m9cd0n9ld/IMU-VR-Full-Body-Tracker/hardware example/TTGO-T7-V1.5_GY-BNO08X_expansion-board/TTGO-T7-V1.5_BNO085_expansion-board.sch

## KiCad design hardware example/TTGO-T7-V1.5_GY-BNO08X_expansion-board/TTGO-T7-V1.5_BNO085_expansion-board.sch (2021-06-28)

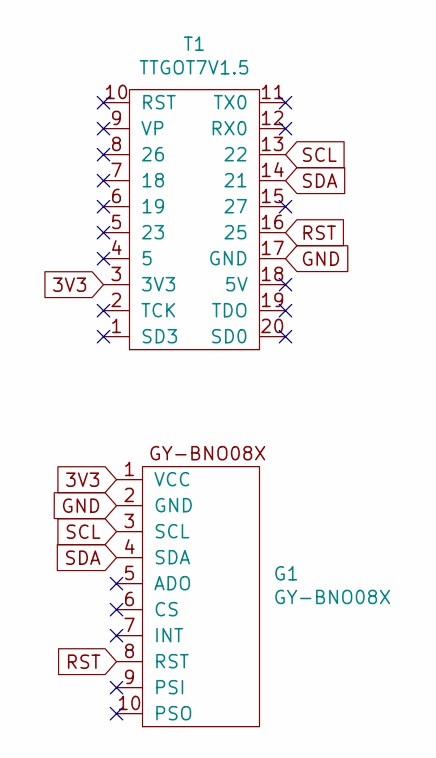
[picture p28: schematic TTGO-T7-V1.5_BNO085_expansion-board.sch]

Parts:
G1: GY-BNO08X
T1: TTGOT7V1.5; TTGO_T7_V1.5

Connections:
3V3: G1.1 (VCC), T1.3 (3V3)
GND: G1.2 (GND), T1.17 (GND)
RST: G1.8 (RST), T1.16 (25)
SCL: G1.3 (SCL), T1.13 (22)
SDA: G1.4 (SDA), T1.14 (21)
