m9cd0n9ld/IMU-VR-Full-Body-Tracker/desktop_server/main.py

import os
import sys
def resource_path(file):
    try:
        directory = os.path.abspath(sys._MEIPASS)
    except:
        directory = os.path.abspath('.')
    return os.path.join(directory, file)

from kivy.config import Config
Config.set('graphics', 'maxfps', '5000')
Config.set('input', 'mouse', 'mouse,disable_multitouch')
Config.set('graphics', 'width', '900')
Config.set('graphics', 'height', '700')
Config.set('graphics', 'minimum_width', '900')
Config.set('graphics', 'minimum_height', '700')
Config.set('kivy', 'window_icon', resource_path('icon.png'))
from kivy.app import App
from kivy.lang import Builder
from kivy.uix.boxlayout import BoxLayout
from kivy.uix.floatlayout import FloatLayout
from kivy.uix.popup import Popup
from kivy.uix.label import Label
from kivy.uix.spinner import Spinner
from kivy.uix.switch import Switch
from kivy.uix.tabbedpanel import TabbedPanel, TabbedPanelItem
from kivy.uix.image import Image
from kivy.clock import Clock, mainthread
from kivy.properties import ObjectProperty
from kivy.core.window import Window
from plyer import filechooser
import serial
import serial.tools.list_ports
from configparser import ConfigParser
import threading
import socket
import struct
import binascii
import time
import math
import subprocess

VERSION = "0.7"

ROLE = ['No role',
        'Left foot',
        'Right foot',
        'Left lower leg',
        'Right lower leg',
        'Left thigh',
        'Right thigh',
        'Waist',
        'Chest',
        'Left shoulder',
        'Right shoulder',
        'Left upper arm',
        'Right upper arm']

MODE = ['AR/VR Stabilized Rotation Vector', 'AR/VR Stabilized Game Rotation Vector']

MODE_SHORT = ['RV', 'GRV']

POWER = [8, 20, 28, 34, 44, 52, 60, 66, 72, 78]

ACCURACY = ['Unreliable', 'Low', 'Medium', 'High']

tpose_image = resource_path('T-pose_skeleton_diagram.png')
kinematics_image = resource_path('tracker_kinematic_chain.png')

def battPercent(v):
    v = float(v)
    denominator = (1 + (v / 3.7)**80)**0.165
    percent = int(123 - 123 / denominator)
    if percent >= 100:
        percent = 100
    elif percent <= 0:
        percent = 0
    return percent

def mapRange(value, inMin=-32767.0, inMax=32767.0, outMin=-1.0, outMax=1.0):
    return outMin + (((value - inMin) / (inMax - inMin)) * (outMax - outMin))

class TrackerView:
    ac = ObjectProperty()
    px = ObjectProperty()
    py = ObjectProperty()
    pz = ObjectProperty()
    qx = ObjectProperty()
    qy = ObjectProperty()
    qz = ObjectProperty()
    qw = ObjectProperty()

class TransformInput:
    tx = ObjectProperty()
    ty = ObjectProperty()
    tz = ObjectProperty()

class SegmentSlider:
    slider = ObjectProperty()
    
class OffsetSlider:
    slider1 = ObjectProperty()
    slider2 = ObjectProperty()
    
class OnOffSwitch:
    switch = ObjectProperty()
    
class Pop(FloatLayout):
    def __init__(self):
        super().__init__()
        self.size = (Window.size[1] * 0.8, Window.size[1] * 0.8)
        self.pos_hint = {'center_x': .5, 'center_y': .5}
        panel = TabbedPanel(do_default_tab=False,
                            size=(Window.size[1] * 0.8, Window.size[1] * 0.8),
                            pos_hint={'center_x': .5, 'center_y': .5},
                            tab_width=Window.size[1] * 0.8 / 2.1)
        
        panelOne = TabbedPanelItem(text='T-pose skeleton joint diagram')
        image_path = tpose_image
        img = Image(source=image_path, pos_hint = {'center_x': .5, 'center_y': .5})
        panelOne.add_widget(img)
        
        panelTwo = TabbedPanelItem(text='Tracker kinematic chain')
        image_path = kinematics_image
        img = Image(source=image_path, pos_hint = {'center_x': .5, 'center_y': .5})
        panelTwo.add_widget(img)

        panel.add_widget(panelOne)
        panel.add_widget(panelTwo)
        
        self.add_widget(panel)

class RoleList(BoxLayout):
    def __init__(self, mac, connect, mode, power, sleep, role):
        super().__init__()
        self.height = App.get_running_app().root.ids.layout_ref.height / 1.75
        self.size_hint_y = None
        self.padding = [0, 0, 0, 2]
        extend = '_extend' in mac
        L1 = Label(size_hint_x=0.2, text=str(mac))
        C1 = Switch(size_hint_x=0.1, active=connect, disabled=extend)
        S1 = Spinner(size_hint_x=0.35, text=str(mode), values=MODE)
        S2 = Spinner(size_hint_x=0.1, text=str(power), values=['{:.1f}'.format(x/4.0) for x in POWER], disabled=extend)
        C2 = Switch(size_hint_x=0.1, active=sleep, disabled=extend)
        S3 = Spinner(size_hint_x=0.15, text=str(role), values=ROLE)
        App.get_running_app().root.ids[mac + '_role_mac'] = L1
        App.get_running_app().root.ids[mac + '_role_connect'] = C1
        App.get_running_app().root.ids[mac + '_role_mode'] = S1
        App.get_running_app().root.ids[mac + '_role_power'] = S2
        App.get_running_app().root.ids[mac + '_role_sleep'] = C2
        App.get_running_app().root.ids[mac + '_role_role'] = S3
        C1.bind(active=self.onActive1)
        S1.bind(text=self.onText1)
        S2.bind(text=self.onText2)
        C2.bind(active=self.onActive2)
        S3.bind(text=self.onText3)
        self.add_widget(L1)
        self.add_widget(C1)
        self.add_widget(S1)
        self.add_widget(S2)
        self.add_widget(C2)
        self.add_widget(S3)
                
    def onActive1(self, instance, value):
        for k, v in App.get_running_app().root.ids.items():
            if '_main' in k and v == instance:
                mac = k.replace('_role_connect', '')
                ImuFbtServer.devices_list[mac]['connect'] = value
                if mac.replace('_main', '_extend') in ImuFbtServer.devices_list.keys() and \
                    mac.replace('_main', '_extend_role_connect') in App.get_running_app().root.ids.keys():
                    App.get_running_app().root.ids[mac.replace('_main', '_extend_role_connect')].active = value
                    ImuFbtServer.devices_list[mac.replace('_main', '_extend')]['connect'] = value
                    
    def onText1(self, instance, value):
        for k, v in App.get_running_app().root.ids.items():
            if v == instance:
                mac = k.replace('_role_mode', '')
                ImuFbtServer.devices_list[mac]['mode'] = value
                
    def onText2(self, instance, value):
        for k, v in App.get_running_app().root.ids.items():
            if '_main' in k and v == instance:
                mac = k.replace('_role_power', '')
                ImuFbtServer.devices_list[mac]['power'] = value
                if mac.replace('_main', '_extend') in ImuFbtServer.devices_list.keys() and \
                    mac.replace('_main', '_extend_role_power') in App.get_running_app().root.ids.keys():
                    App.get_running_app().root.ids[mac.replace('_main', '_extend_role_power')].text = value
                    ImuFbtServer.devices_list[mac.replace('_main', '_extend')]['power'] = value
                    
    def onActive2(self, instance, value):
        for k, v in App.get_running_app().root.ids.items():
            if '_main' in k and v == instance:
                mac = k.replace('_role_sleep', '')
                ImuFbtServer.devices_list[mac]['sleep'] = value
                if mac.replace('_main', '_extend') in ImuFbtServer.devices_list.keys() and \
                    mac.replace('_main', '_extend_role_sleep') in App.get_running_app().root.ids.keys():
                    App.get_running_app().root.ids[mac.replace('_main', '_extend_role_sleep')].active = value
                    ImuFbtServer.devices_list[mac.replace('_main', '_extend')]['sleep'] = value

    def onText3(self, instance, value):
        for k, v in App.get_running_app().root.ids.items():
            if v == instance:
                mac = k.replace('_role_role', '')
                ImuFbtServer.devices_list[mac]['role'] = value

class DeviceList(BoxLayout):
    def __init__(self, mac, ip, battery, mode, accuracy, power, sleep, role):
        super().__init__()
        self.height = App.get_running_app().root.ids.layout_ref.height / 1.75
        self.size_hint_y = None
        self.padding = [0, 0, 0, 2]
        L1 = Label(size_hint_x=0.2, text=str(mac))
        L2 = Label(size_hint_x=0.175, text=str(ip))
        L3 = Label(size_hint_x=0.075, text=str(battery))
        L4 = Label(size_hint_x=0.075, text=str(battPercent(battery)))
        L5 = Label(size_hint_x=0.075, text=str(mode))
        L6 = Label(size_hint_x=0.075, text=str(accuracy))
        L7 = Label(size_hint_x=0.0875, text=str(power))
        L8 = Label(size_hint_x=0.0875, text=str(sleep))
        L9 = Label(size_hint_x=0.15, text=str(role))
        App.get_running_app().root.ids[mac + '_list_mac'] = L1
        App.get_running_app().root.ids[mac + '_list_ip'] = L2
        App.get_running_app().root.ids[mac + '_list_battery'] = L3
        App.get_running_app().root.ids[mac + '_list_percent'] = L4
        App.get_running_app().root.ids[mac + '_list_mode'] = L5
        App.get_running_app().root.ids[mac + '_list_accuracy'] = L6
        App.get_running_app().root.ids[mac + '_list_power'] = L7
        App.get_running_app().root.ids[mac + '_list_sleep'] = L8
        App.get_running_app().root.ids[mac + '_list_role'] = L9
        self.add_widget(L1)
        self.add_widget(L2)
        self.add_widget(L3)
        self.add_widget(L4)
        self.add_widget(L5)
        self.add_widget(L6)
        self.add_widget(L7)
        self.add_widget(L8)
        self.add_widget(L9)

class ImuFbtServer(App):
    broadPort = 6969
    
    devices_list = {}
    devices_online = {}
    devices_broad_online = {}

    focused = False
    temp_focus = ''
    
    current_page = ''
    
    def save_settings(self):
        filechooser.save_file(on_selection=self.handle_save, filters=['*.ini'])
    
    def load_settings(self):
        filechooser.open_file(on_selection=self.handle_load, filters=['*.ini'])
        
    def handle_save(self, selection):
        if len(selection):
            file = selection[0]
            if file[-4:] != '.ini':
                file += '.ini'
            self.save(file)
        
    def handle_load(self, selection):
        if len(selection):
            self.load(selection[0])
    
    def show_popup(self):
        show = Pop()
        size = (Window.size[1] * 0.8, Window.size[1] * 0.8)
        popupWindow = Popup(title="Help", content=show, size_hint=(None, None), size=size)
        popupWindow.open()

    @mainthread
    def textinput_focus(self, *args):
        instance = args[0][0]
        value = args[0][1]
        if value:
            self.focused = True
            self.temp_focus = instance.text
            Clock.schedule_once(lambda dt: instance.select_all())
        else:
            if instance.text == '':
                instance.text = self.temp_focus
            self.focused = False
    
    @mainthread
    def wifi_configure_disabled(self, val):
        self.root.ids.wifi_configure.disabled = val
    
    @mainthread
    def wifi_configure_status_text(self, val):
        self.root.ids.wifi_configure_status.text = val
    
    def wifi_thread(self):
        self.wifi_configure_disabled(True)
        try:
            port = self.root.ids.com_port_list.text
            ssid = self.root.ids.wifi_ssid.text
            password = self.root.ids.wifi_password.text
            if len(port) == 0 or len(ssid) == 0 or len(password) == 0:
                self.wifi_configure_status_text('Invalid settings')
                self.wifi_configure_disabled(False)
                return
            ser = serial.Serial(port, 115200, timeout=0.1, write_timeout=0.1,
                                xonxoff=False, rtscts=False, dsrdtr=False)
            payload = '111\n{}\n{}\n'.format(ssid, password)
            ser.write(payload.encode())
            start = time.perf_counter()
            while self.wifi_thread_run:
                msg = ser.read(1)
                if len(msg) > 0 and msg[0] == 110:
                    self.wifi_configure_status_text('WiFi configured')
                    break
                if time.perf_counter() - start >= 3:
                    self.wifi_configure_status_text('Serial timeout error')
                    break
                time.sleep(0.1)
            ser.close()
        except:
            self.wifi_configure_status_text('Serial connection error')
        self.wifi_configure_disabled(False)
        self.wifi_thread_run = False
        
    def configure_wifi(self):
        self.wifi_thread_run = True
        self.wifi_thread_process = threading.Thread(target=self.wifi_thread, args=())
        self.wifi_thread_process.start()
        
    def com_port_scanner(self, dt):
        com_list = serial.tools.list_ports.comports()
        port_list = []
        for port in com_list:
            port_list.append(port[0])
        if self.root.ids.com_port_list.text not in port_list:
            self.root.ids.com_port_list.text = ''
        self.root.ids.com_port_list.values = port_list
    
    @mainthread
    def calibrate_imu_button_disabled(self, val):
        self.root.ids.calibrate_imu_button.disabled = val
    
    @mainthread
    def calibrate_imu_button_text(self, val):
        self.root.ids.calibrate_imu_button.text = val
    
    def calibrate(self):
        self.calibrate_imu_button_disabled(True)
        i = 3
        while self.calibrate_run:
            self.calibrate_imu_button_text('Calibrating in {}...'.format(i))
            i -= 1
            time.sleep(1)
            if i <= 0:
                payload = struct.pack('<B', 51)
                if self.bridgePort != 0:
                    self.sock_listen.sendto(self.wrap_payload(payload), ('127.0.0.1', self.bridgePort))
                break
        self.calibrate_run = False
        self.calibrate_imu_button_text('Calibrate')
        self.calibrate_imu_button_disabled(False)
    
    def calibrate_imu(self):
        self.calibrate_run = True
        self.calibrate_process = threading.Thread(target=self.calibrate, args=())
        self.calibrate_process.start()
        
    def measure_height(self):
        payload = struct.pack('<B', 31)
        if self.bridgePort != 0:
            self.sock_listen.sendto(self.wrap_payload(payload), ('127.0.0.1', self.bridgePort))
        
    def check_payload(self, payload):
        if payload[0] == ord('I') and payload[-1] == ord('i'):
            return True
        else:
            return False
        
    def wrap_payload(self, payload):
        header = b'I'
        footer = b'i'
        return header + payload + footer
    
    def unwrap_payload(self, payload):
        return payload[1:-1]
    
    @mainthread
    def add_stack_role(self, mac, connect, mode, power, sleep, role):
        RoleList_widget = RoleList(mac, connect, mode, power, sleep, role)
        self.root.ids.stack_role.add_widget(RoleList_widget)
        self.root.ids[mac + '_role'] = RoleList_widget
        
    @mainthread
    def remove_stack_role(self, k):
        if k + '_role' in self.root.ids.keys():
            self.root.ids.stack_role.remove_widget(self.root.ids[k + '_role'])
        if k + '_role' in self.root.ids.keys():
            del self.root.ids[k + '_role']
        if k + '_role_mac' in self.root.ids.keys():
            del self.root.ids[k + '_role_mac']
        if k + '_role_connect' in self.root.ids.keys():
            del self.root.ids[k + '_role_connect']
        if k + '_role_mode' in self.root.ids.keys():
            del self.root.ids[k + '_role_mode']
        if k + '_role_power' in self.root.ids.keys():
            del self.root.ids[k + '_role_power']
        if k + '_role_sleep' in self.root.ids.keys():
            del self.root.ids[k + '_role_sleep']
        if k + '_role_role' in self.root.ids.keys():
            del self.root.ids[k + '_role_role']
        
    @mainthread
    def steam_status_text(self, val):
        self.root.ids.steam_status.text = val
    
    def broadudp(self):
        broad_listen = socket.socket(socket.AF_INET, socket.SOCK_DGRAM)
        broad_listen.setsockopt(socket.SOL_SOCKET, socket.SO_REUSEADDR, 1)
        broad_listen.bind(('0.0.0.0', self.broadPort))
        broad_listen.settimeout(0.5)
        
        hostname = socket.gethostname()
        host_list = socket.getaddrinfo(hostname, self.broadPort, socket.AF_INET, socket.SOCK_DGRAM)
        hostIPs = ['127.0.0.1']
        for i in range(len(host_list)):
            hostIPs.append(host_list[i][4][0])
        
        while self.broad_run:
            try:
                payload, addr = broad_listen.recvfrom(32)
                if self.check_payload(payload):
                    payload = self.unwrap_payload(payload)
                    if len(payload) == struct.calcsize('<BBBBBBB?'):
                        if payload[0] == 77:
                            ip = addr[0]
                            mac = binascii.hexlify(payload[1:7]).decode()
                            extend = payload[7]
                            macs = [mac + '_main', mac + '_extend']
                            roles_reply = [0, 0]
                            modes_reply = [0, 0]
                            if extend:
                                for_length = 2
                            else:
                                for_length = 1
                            for i in range(for_length):
                                mac = macs[i]
                                self.devices_broad_online[mac] = time.perf_counter()
                                if mac + '_role' not in self.root.ids.keys():
                                    if mac in self.devices_list.keys():
                                        connect = self.devices_list[mac]['connect']
                                        mode = self.devices_list[mac]['mode']
                                        power = self.devices_list[mac]['power']
                                        sleep = self.devices_list[mac]['sleep']
                                        role = self.devices_list[mac]['role']
                                    else:
                                        connect = False
                                        mode = MODE[0]
                                        power = '19.5'
                                        sleep = True
                                        role = ROLE[0]
                                        self.devices_list[mac] = {}
                                        self.devices_list[mac]['connect'] = connect
                                        self.devices_list[mac]['mode'] = mode
                                        self.devices_list[mac]['power'] = power
                                        self.devices_list[mac]['sleep'] = sleep
                                        self.devices_list[mac]['role'] = role
                                    self.add_stack_role(mac, connect, mode, power, sleep, role)
                                roles_reply[i] = ROLE.index(self.devices_list[mac]['role'])
                                modes_reply[i] = MODE.index(self.devices_list[mac]['mode'])
                            if self.devices_list[macs[0]]['connect']:
                                reply = struct.pack('<BBBBBBBHH', 200, roles_reply[0], roles_reply[1], modes_reply[0], modes_reply[1], 
                                                    int(float(self.devices_list[mac]['power']) * 4), self.devices_list[mac]['sleep'], 
                                                    self.serverPort, self.bridgePort)
                                broad_listen.sendto(self.wrap_payload(reply), (ip, self.broadPort))
                    elif len(payload) == struct.calcsize('<BH'):
                        if payload[0] == 17 and addr[0] in hostIPs:
                            self.steam_status_text('SteamVR online')
                            ip = addr[0]
                            _, self.bridgePort = struct.unpack('<BH', payload)
                            reply = struct.pack('<BH', 18, self.serverPort)
                            broad_listen.sendto(self.wrap_payload(reply), (ip, self.bridgePort))
            except:
                pass
            to_del = []
            for k, v in self.devices_broad_online.items():
                if time.perf_counter() - v >= 5:
                    to_del.append(k)
            for k in to_del:
                if k in self.devices_broad_online.keys():
                    del self.devices_broad_online[k]
                self.remove_stack_role(k)
        broad_listen.close()
        
    @mainthread
    def add_stack_list(self, mac, ip, battery, mode, accuracy, power ,sleep, role):
        DeviceList_widget = DeviceList(mac, ip, battery, mode, accuracy, power ,sleep, role)
        self.root.ids.stack_list.add_widget(DeviceList_widget)
        self.root.ids[mac + '_list'] = DeviceList_widget
        
    @mainthread
    def edit_stack_list(self, mac, ip, battery, mode, accuracy, power ,sleep, role):
        self.root.ids[mac + '_list_mac'].text = str(mac)
        self.root.ids[mac + '_list_ip'].text = str(ip)
        self.root.ids[mac + '_list_battery'].text = str(battery)
        self.root.ids[mac + '_list_percent'].text = str(battPercent(battery))
        self.root.ids[mac + '_list_mode'].text = str(mode)
        self.root.ids[mac + '_list_accuracy'].text = str(accuracy)
        self.root.ids[mac + '_list_power'].text = str(power)
        self.root.ids[mac + '_list_sleep'].text = str(sleep)
        self.root.ids[mac + '_list_role'].text = str(role)
        
    @mainthread
    def remove_stack_list(self, k):
        if k + '_list' in self.root.ids.keys():
            self.root.ids.stack_list.remove_widget(self.root.ids[k + '_list'])
        if k + '_list' in self.root.ids.keys():
            del self.root.ids[k + '_list']
        if k + '_list_mac' in self.root.ids.keys():
            del self.root.ids[k + '_list_mac']
        if k + '_list_ip' in self.root.ids.keys():
            del self.root.ids[k + '_list_ip']
        if k + '_list_battery' in self.root.ids.keys():
            del self.root.ids[k + '_list_battery']
        if k + '_list_percent' in self.root.ids.keys():
            del self.root.ids[k + '_list_percent']
        if k + '_list_mode' in self.root.ids.keys():
            del self.root.ids[k + '_list_mode']
        if k + '_list_accuracy' in self.root.ids.keys():
            del self.root.ids[k + '_list_accuracy']
        if k + '_list_power' in self.root.ids.keys():
            del self.root.ids[k + '_list_power']
        if k + '_list_sleep' in self.root.ids.keys():
            del self.root.ids[k + '_list_sleep']
        if k + '_list_role' in self.root.ids.keys():
            del self.root.ids[k + '_list_role']
    
    @mainthread
    def headset_height_text(self, val):
        self.root.ids.headset_height.text = val
        
    @mainthread
    def on_tracker_data(self, payload):
        if payload[0] in range(1, 13) and self.current_page == 'Tracker Data':
            tracker_type = 'tracker_{}'.format(payload[0])
            _, ac, px, py, pz, qx, qy, qz, qw, _ = struct.unpack('<B?fffhhhhB', payload)
            self.root.ids[tracker_type].ac.text = str(ac)
            self.root.ids[tracker_type].px.text = '{:.2f}'.format(px)
            self.root.ids[tracker_type].py.text = '{:.2f}'.format(py)
            self.root.ids[tracker_type].pz.text = '{:.2f}'.format(pz)
            self.root.ids[tracker_type].qx.text = '{:.2f}'.format(mapRange(qx))
            self.root.ids[tracker_type].qy.text = '{:.2f}'.format(mapRange(qy))
            self.root.ids[tracker_type].qz.text = '{:.2f}'.format(mapRange(qz))
            self.root.ids[tracker_type].qw.text = '{:.2f}'.format(mapRange(qw))
        
    def udp(self):
        self.sock_listen = socket.socket(socket.AF_INET, socket.SOCK_DGRAM)
        self.sock_listen.bind(('0.0.0.0', 0))
        self.sock_listen.settimeout(0.5)
        self.serverPort = self.sock_listen.getsockname()[1]
        t_tx_driver = time.perf_counter()
        while self.thread_run:
            try:
                payload, addr = self.sock_listen.recvfrom(32)
                if self.check_payload(payload):
                    payload = self.unwrap_payload(payload)
                    if len(payload) == struct.calcsize('<Bf'):
                        if payload[0] == 32:
                            height = struct.unpack('<f', payload[1:])[0]
                            self.headset_height_text('{:.2f} m'.format(height))
                    elif len(payload) == struct.calcsize('<BH'):
                        if payload[0] == 87:
                            self.steam_status_text('SteamVR online')
                            _, self.bridgePort = struct.unpack('<BH', payload)
                            self.set_driver_settings()
                            t_tx_driver = time.perf_counter()
                        elif payload[0] == 97:
                            self.steam_status_text('SteamVR online')
                            _, self.bridgePort = struct.unpack('<BH', payload)
                            self.set_init_settings()
                            t_tx_driver = time.perf_counter()
                    elif len(payload) == struct.calcsize('<B?fffhhhhB'):
                        self.on_tracker_data(payload)
                    elif len(payload) == struct.calcsize('<BBBBBBBBfBBBBBB?'):
                        mac = binascii.hexlify(payload[2:8]).decode()
                        ip = addr[0]
                        battery, mode, mode_ext, accuracy, accuracy_ext, power, sleep, extend = struct.unpack('<fBBBBBB?', payload[8:])
                        battery = '{:.2f}'.format(battery)
                        power = '{:.1f}'.format(power/4.0)
                        sleep = str(bool(sleep))
                        roles_reply = [0, 0]
                        modes_reply = [0, 0]
                        if extend:
                            for_length = 2
                            roles = [ROLE[payload[0]], ROLE[payload[1]]]
                            modes = [MODE_SHORT[mode], MODE_SHORT[mode_ext]]
                            accuracies = [ACCURACY[accuracy], ACCURACY[accuracy_ext]]
                            macs = [mac + '_main', mac + '_extend']
                        else:
                            for_length = 1
                            roles = [ROLE[payload[0]]]
                            modes = [MODE_SHORT[mode]]
                            accuracies = [ACCURACY[accuracy]]
                            macs = [mac + '_main']
                        for i in range(for_length):
                            role = roles[i]
                            mode = modes[i]
                            accuracy = accuracies[i]
                            mac = macs[i]
                            self.devices_online[mac] = time.perf_counter()
                            self.devices_broad_online[mac] = time.perf_counter()
                            if mac + '_list' not in self.root.ids.keys():
                                self.add_stack_list(mac, ip, battery, mode, accuracy, power, sleep, role)
                            else:
                                self.edit_stack_list(mac, ip, battery, mode, accuracy, power, sleep, role)
                            roles_reply[i] = ROLE.index(self.devices_list[mac]['role'])
                            modes_reply[i] = MODE.index(self.devices_list[mac]['mode'])
                        if self.devices_list[macs[0]]['connect']:
                            reply = struct.pack('<BBBBBBBHH', 200, roles_reply[0], roles_reply[1], modes_reply[0], modes_reply[1], 
                                                int(float(self.devices_list[mac]['power']) * 4), self.devices_list[mac]['sleep'], 
                                                self.serverPort, self.bridgePort)
                            self.sock_listen.sendto(self.wrap_payload(reply), (ip, self.broadPort))
            except:
                pass
            if time.perf_counter() - t_tx_driver >= 5:
                self.steam_status_text('SteamVR offline')
                self.bridgePort = 0
            to_del = []
            for k, v in self.devices_online.items():
                if time.perf_counter() - v >= 5:
                    to_del.append(k)
            for k in to_del:
                if k in self.devices_online.keys():
                    del self.devices_online[k]
                self.remove_stack_list(k)
        self.sock_listen.close()
        
    def onTabChange(self, tab):
        self.current_page = tab.text
        if tab.text == 'Tracker Data':
            if self.bridgePort != 0:
                payload = struct.pack('<B', 171)
                self.sock_listen.sendto(self.wrap_payload(payload), ('127.0.0.1', self.bridgePort))
        else:
            if self.bridgePort != 0:
                payload = struct.pack('<B', 172)
                self.sock_listen.sendto(self.wrap_payload(payload), ('127.0.0.1', self.bridgePort))

    def set_driver_settings(self):
        T_lfoot_drv = [math.radians(float(self.root.ids.lfoot_t.tx.text)),
                       math.radians(float(self.root.ids.lfoot_t.ty.text)),
                       math.radians(float(self.root.ids.lfoot_t.tz.text))]
        T_rfoot_drv = [math.radians(float(self.root.ids.rfoot_t.tx.text)),
                       math.radians(float(self.root.ids.rfoot_t.ty.text)),
                       math.radians(float(self.root.ids.rfoot_t.tz.text))]
        T_lshin_drv = [math.radians(float(self.root.ids.lshin_t.tx.text)),
                       math.radians(float(self.root.ids.lshin_t.ty.text)),
                       math.radians(float(self.root.ids.lshin_t.tz.text))]
        T_rshin_drv = [math.radians(float(self.root.ids.rshin_t.tx.text)),
                       math.radians(float(self.root.ids.rshin_t.ty.text)),
                       math.radians(float(self.root.ids.rshin_t.tz.text))]
        T_lthigh_drv = [math.radians(float(self.root.ids.lthigh_t.tx.text)),
                        math.radians(float(self.root.ids.lthigh_t.ty.text)),
                        math.radians(float(self.root.ids.lthigh_t.tz.text))]
        T_rthigh_drv = [math.radians(float(self.root.ids.rthigh_t.tx.text)),
                        math.radians(float(self.root.ids.rthigh_t.ty.text)),
                        math.radians(float(self.root.ids.rthigh_t.tz.text))]
        T_waist_drv = [math.radians(float(self.root.ids.waist_t.tx.text)),
                       math.radians(float(self.root.ids.waist_t.ty.text)),
                       math.radians(float(self.root.ids.waist_t.tz.text))]
        T_chest_drv = [math.radians(float(self.root.ids.chest_t.tx.text)),
                       math.radians(float(self.root.ids.chest_t.ty.text)),
                       math.radians(float(self.root.ids.chest_t.tz.text))]
        T_lshoulder_drv = [math.radians(float(self.root.ids.lshoulder_t.tx.text)),
                           math.radians(float(self.root.ids.lshoulder_t.ty.text)),
                           math.radians(float(self.root.ids.lshoulder_t.tz.text))]
        T_rshoulder_drv = [math.radians(float(self.root.ids.rshoulder_t.tx.text)),
                           math.radians(float(self.root.ids.rshoulder_t.ty.text)),
                           math.radians(float(self.root.ids.rshoulder_t.tz.text))]
        T_lupperarm_drv = [math.radians(float(self.root.ids.lupperarm_t.tx.text)),
                           math.radians(float(self.root.ids.lupperarm_t.ty.text)),
                           math.radians(float(self.root.ids.lupperarm_t.tz.text))]
        T_rupperarm_drv = [math.radians(float(self.root.ids.rupperarm_t.tx.text)),
                           math.radians(float(self.root.ids.rupperarm_t.ty.text)),
                           math.radians(float(self.root.ids.rupperarm_t.tz.text))]
        shin_h = float(self.root.ids.shin_h.slider.value * self.root.ids.vscale.slider.value)
        thigh_h = float(self.root.ids.thigh_h.slider.value * self.root.ids.vscale.slider.value)
        lback_h = float(self.root.ids.lback_h.slider.value * self.root.ids.vscale.slider.value)
        uback_h = float(self.root.ids.uback_h.slider.value * self.root.ids.vscale.slider.value)
        head_h = float(self.root.ids.head_h.slider.value * self.root.ids.vscale.slider.value)
        shoulder_h = float(self.root.ids.shoulder_h.slider.value * self.root.ids.vscale.slider.value)
        hip_width_h = float(self.root.ids.hip_width_h.slider.value * self.root.ids.hscale.slider.value)
        shoulder_width_h = float(self.root.ids.shoulder_width_h.slider.value * self.root.ids.hscale.slider.value)
        foot_sensor_h = float(self.root.ids.foot_sensor_h.slider.value)
        shin_sensor_h = float(self.root.ids.shin_sensor_h.slider.value)
        thigh_sensor_h = float(self.root.ids.thigh_sensor_h.slider.value)
        waist_sensor_h = float(self.root.ids.waist_sensor_h.slider.value)
        chest_sensor_h = float(self.root.ids.chest_sensor_h.slider.value)
        shoulder_sensor_h = float(self.root.ids.shoulder_sensor_h.slider.value)
        upperarm_sensor_h = float(self.root.ids.upperarm_sensor_h.slider.value)
        floor_offset = float(self.root.ids.floor_offset.slider.value)
        override_feet = self.root.ids.override_feet_en_check.switch.active
        payload = bytearray(209)
        struct.pack_into('<3f', payload, 0, *T_lfoot_drv)
        struct.pack_into('<3f', payload, 12, *T_rfoot_drv)
        struct.pack_into('<3f', payload, 24, *T_lshin_drv)
        struct.pack_into('<3f', payload, 36, *T_rshin_drv)
        struct.pack_into('<3f', payload, 48, *T_lthigh_drv)
        struct.pack_into('<3f', payload, 60, *T_rthigh_drv)
        struct.pack_into('<3f', payload, 72, *T_waist_drv)
        struct.pack_into('<3f', payload, 84, *T_chest_drv)
        struct.pack_into('<3f', payload, 96, *T_lshoulder_drv)
        struct.pack_into('<3f', payload, 108, *T_rshoulder_drv)
        struct.pack_into('<3f', payload, 120, *T_lupperarm_drv)
        struct.pack_into('<3f', payload, 132, *T_rupperarm_drv)
        struct.pack_into('<16f', payload, 144,
                         shin_h,
                         thigh_h,
                         lback_h,
                         uback_h,
                         head_h,
                         shoulder_h,
                         hip_width_h,
                         shoulder_width_h,
                         foot_sensor_h,
                         shin_sensor_h,
                         thigh_sensor_h,
                         waist_sensor_h,
                         chest_sensor_h,
                         shoulder_sensor_h,
                         upperarm_sensor_h,
                         floor_offset)
        struct.pack_into('<?', payload, 208, override_feet)
        if not self.focused and self.bridgePort != 0:
            self.sock_listen.sendto(self.wrap_payload(payload), ('127.0.0.1', self.bridgePort))
        
        lfoot_1 = float(self.root.ids.lfoot_o.slider1.value)
        lfoot_2 = float(self.root.ids.lfoot_o.slider2.value)
        rfoot_1 = float(self.root.ids.rfoot_o.slider1.value)
        rfoot_2 = float(self.root.ids.rfoot_o.slider2.value)
        lshin_1 = float(self.root.ids.lshin_o.slider1.value)
        lshin_2 = float(self.root.ids.lshin_o.slider2.value)
        rshin_1 = float(self.root.ids.rshin_o.slider1.value)
        rshin_2 = float(self.root.ids.rshin_o.slider2.value)
        lthigh_1 = float(self.root.ids.lthigh_o.slider1.value)
        lthigh_2 = float(self.root.ids.lthigh_o.slider2.value)
        rthigh_1 = float(self.root.ids.rthigh_o.slider1.value)
        rthigh_2 = float(self.root.ids.rthigh_o.slider2.value)
        waist_1 = float(self.root.ids.waist_o.slider1.value)
        waist_2 = float(self.root.ids.waist_o.slider2.value)
        chest_1 = float(self.root.ids.chest_o.slider1.value)
        chest_2 = float(self.root.ids.chest_o.slider2.value)
        lshoulder_1 = float(self.root.ids.lshoulder_o.slider1.value)
        lshoulder_2 = float(self.root.ids.lshoulder_o.slider2.value)
        rshoulder_1 = float(self.root.ids.rshoulder_o.slider1.value)
        rshoulder_2 = float(self.root.ids.rshoulder_o.slider2.value)
        lupperarm_1 = float(self.root.ids.lupperarm_o.slider1.value)
        lupperarm_2 = float(self.root.ids.lupperarm_o.slider2.value)
        rupperarm_1 = float(self.root.ids.rupperarm_o.slider1.value)
        rupperarm_2 = float(self.root.ids.rupperarm_o.slider2.value)
        head_1 = float(self.root.ids.head_o.slider1.value)
        head_2 = float(self.root.ids.head_o.slider2.value)
        payload = bytearray(104)
        struct.pack_into('<2f', payload, 0, lfoot_1, lfoot_2)
        struct.pack_into('<2f', payload, 8, rfoot_1, rfoot_2)
        struct.pack_into('<2f', payload, 16, lshin_1, lshin_2)
        struct.pack_into('<2f', payload, 24, rshin_1, rshin_2)
        struct.pack_into('<2f', payload, 32, lthigh_1, lthigh_2)
        struct.pack_into('<2f', payload, 40, rthigh_1, rthigh_2)
        struct.pack_into('<2f', payload, 48, waist_1, waist_2)
        struct.pack_into('<2f', payload, 56, chest_1, chest_2)
        struct.pack_into('<2f', payload, 64, lshoulder_1, lshoulder_2)
        struct.pack_into('<2f', payload, 72, rshoulder_1, rshoulder_2)
        struct.pack_into('<2f', payload, 80, lupperarm_1, lupperarm_2)
        struct.pack_into('<2f', payload, 88, rupperarm_1, rupperarm_2)
        struct.pack_into('<2f', payload, 96, head_1, head_2)
        if self.bridgePort != 0:
            self.sock_listen.sendto(self.wrap_payload(payload), ('127.0.0.1', self.bridgePort))
        
    def set_init_settings(self):
        feet_enable = self.root.ids.feet_en_check.switch.active
        shin_enable = self.root.ids.shin_en_check.switch.active
        thigh_enable = self.root.ids.thigh_en_check.switch.active
        waist_enable = self.root.ids.waist_en_check.switch.active
        chest_enable = self.root.ids.chest_en_check.switch.active
        shoulder_enable = self.root.ids.shoulder_en_check.switch.active
        upperarm_enable = self.root.ids.upperarm_en_check.switch.active
        payload = struct.pack('<7B', 
                              feet_enable,
                              shin_enable,
                              thigh_enable,
                              waist_enable,
                              chest_enable,
                              shoulder_enable,
                              upperarm_enable)
        if self.bridgePort != 0:
            self.sock_listen.sendto(self.wrap_payload(payload), ('127.0.0.1', self.bridgePort))
    
    @mainthread
    def save(self, file):        
        config = ConfigParser()
        
        config.add_section('version')
        config.set('version', 'version', VERSION)
        
        config.add_section('lfoot')
        config.set('lfoot', 'x', self.root.ids.lfoot_t.tx.text)
        config.set('lfoot', 'y', self.root.ids.lfoot_t.ty.text)
        config.set('lfoot', 'z', self.root.ids.lfoot_t.tz.text)
        
        config.add_section('rfoot')
        config.set('rfoot', 'x', self.root.ids.rfoot_t.tx.text)
        config.set('rfoot', 'y', self.root.ids.rfoot_t.ty.text)
        config.set('rfoot', 'z', self.root.ids.rfoot_t.tz.text)

        config.add_section('lshin')
        config.set('lshin', 'x', self.root.ids.lshin_t.tx.text)
        config.set('lshin', 'y', self.root.ids.lshin_t.ty.text)
        config.set('lshin', 'z', self.root.ids.lshin_t.tz.text)

        config.add_section('rshin')
        config.set('rshin', 'x', self.root.ids.rshin_t.tx.text)
        config.set('rshin', 'y', self.root.ids.rshin_t.ty.text)
        config.set('rshin', 'z', self.root.ids.rshin_t.tz.text)

        config.add_section('lthigh')
        config.set('lthigh', 'x', self.root.ids.lthigh_t.tx.text)
        config.set('lthigh', 'y', self.root.ids.lthigh_t.ty.text)
        config.set('lthigh', 'z', self.root.ids.lthigh_t.tz.text)

        config.add_section('rthigh')
        config.set('rthigh', 'x', self.root.ids.rthigh_t.tx.text)
        config.set('rthigh', 'y', self.root.ids.rthigh_t.ty.text)
        config.set('rthigh', 'z', self.root.ids.rthigh_t.tz.text)

        config.add_section('waist')
        config.set('waist', 'x', self.root.ids.waist_t.tx.text)
        config.set('waist', 'y', self.root.ids.waist_t.ty.text)
        config.set('waist', 'z', self.root.ids.waist_t.tz.text)
        
        config.add_section('chest')
        config.set('chest', 'x', self.root.ids.chest_t.tx.text)
        config.set('chest', 'y', self.root.ids.chest_t.ty.text)
        config.set('chest', 'z', self.root.ids.chest_t.tz.text)
        
        config.add_section('lshoulder')
        config.set('lshoulder', 'x', self.root.ids.lshoulder_t.tx.text)
        config.set('lshoulder', 'y', self.root.ids.lshoulder_t.ty.text)
        config.set('lshoulder', 'z', self.root.ids.lshoulder_t.tz.text)
        
        config.add_section('rshoulder')
        config.set('rshoulder', 'x', self.root.ids.rshoulder_t.tx.text)
        config.set('rshoulder', 'y', self.root.ids.rshoulder_t.ty.text)
        config.set('rshoulder', 'z', self.root.ids.rshoulder_t.tz.text)
        
        config.add_section('lupperarm')
        config.set('lupperarm', 'x', self.root.ids.lupperarm_t.tx.text)
        config.set('lupperarm', 'y', self.root.ids.lupperarm_t.ty.text)
        config.set('lupperarm', 'z', self.root.ids.lupperarm_t.tz.text)
        
        config.add_section('rupperarm')
        config.set('rupperarm', 'x', self.root.ids.rupperarm_t.tx.text)
        config.set('rupperarm', 'y', self.root.ids.rupperarm_t.ty.text)
        config.set('rupperarm', 'z', self.root.ids.rupperarm_t.tz.text)

        config.add_section('parameter')
        config.set('parameter', 'shin_h', str(self.root.ids.shin_h.slider.value))
        config.set('parameter', 'thigh_h', str(self.root.ids.thigh_h.slider.value))
        config.set('parameter', 'lback_h', str(self.root.ids.lback_h.slider.value))
        config.set('parameter', 'uback_h', str(self.root.ids.uback_h.slider.value))
        config.set('parameter', 'head_h', str(self.root.ids.head_h.slider.value))
        config.set('parameter', 'shoulder_h', str(self.root.ids.shoulder_h.slider.value))
        config.set('parameter', 'hip_width_h', str(self.root.ids.hip_width_h.slider.value))
        config.set('parameter', 'shoulder_width_h', str(self.root.ids.shoulder_width_h.slider.value))
        config.set('parameter', 'vscale', str(self.root.ids.vscale.slider.value))
        config.set('parameter', 'hscale', str(self.root.ids.hscale.slider.value))
        config.set('parameter', 'foot_sensor_h', str(self.root.ids.foot_sensor_h.slider.value))
        config.set('parameter', 'shin_sensor_h', str(self.root.ids.shin_sensor_h.slider.value))
        config.set('parameter', 'thigh_sensor_h', str(self.root.ids.thigh_sensor_h.slider.value))
        config.set('parameter', 'waist_sensor_h', str(self.root.ids.waist_sensor_h.slider.value))
        config.set('parameter', 'chest_sensor_h', str(self.root.ids.chest_sensor_h.slider.value))
        config.set('parameter', 'shoulder_sensor_h', str(self.root.ids.shoulder_sensor_h.slider.value))
        config.set('parameter', 'upperarm_sensor_h', str(self.root.ids.upperarm_sensor_h.slider.value))
        config.set('parameter', 'floor_offset', str(self.root.ids.floor_offset.slider.value))
        config.set('parameter', 'override_feet_en_check', str(int(self.root.ids.override_feet_en_check.switch.active)))
        
        config.add_section('activation')
        config.set('activation', 'feet_en_check', str(int(self.root.ids.feet_en_check.switch.active)))
        config.set('activation', 'shin_en_check', str(int(self.root.ids.shin_en_check.switch.active)))
        config.set('activation', 'thigh_en_check', str(int(self.root.ids.thigh_en_check.switch.active)))
        config.set('activation', 'waist_en_check', str(int(self.root.ids.waist_en_check.switch.active)))
        config.set('activation', 'chest_en_check', str(int(self.root.ids.chest_en_check.switch.active)))
        config.set('activation', 'shoulder_en_check', str(int(self.root.ids.shoulder_en_check.switch.active)))
        config.set('activation', 'upperarm_en_check', str(int(self.root.ids.upperarm_en_check.switch.active)))

        config.add_section('offset')
        config.set('offset', 'lfoot_pos_1', str(self.root.ids.lfoot_o.slider1.value))
        config.set('offset', 'lfoot_pos_2', str(self.root.ids.lfoot_o.slider2.value))
        config.set('offset', 'rfoot_pos_1', str(self.root.ids.rfoot_o.slider1.value))
        config.set('offset', 'rfoot_pos_2', str(self.root.ids.rfoot_o.slider2.value))
        config.set('offset', 'lshin_pos_1', str(self.root.ids.lshin_o.slider1.value))
        config.set('offset', 'lshin_pos_2', str(self.root.ids.lshin_o.slider2.value))
        config.set('offset', 'rshin_pos_1', str(self.root.ids.rshin_o.slider1.value))
        config.set('offset', 'rshin_pos_2', str(self.root.ids.rshin_o.slider2.value))
        config.set('offset', 'lthigh_pos_1', str(self.root.ids.lthigh_o.slider1.value))
        config.set('offset', 'lthigh_pos_2', str(self.root.ids.lthigh_o.slider2.value))
        config.set('offset', 'rthigh_pos_1', str(self.root.ids.rthigh_o.slider1.value))
        config.set('offset', 'rthigh_pos_2', str(self.root.ids.rthigh_o.slider2.value))
        config.set('offset', 'waist_pos_1', str(self.root.ids.waist_o.slider1.value))
        config.set('offset', 'waist_pos_2', str(self.root.ids.waist_o.slider2.value))
        config.set('offset', 'chest_pos_1', str(self.root.ids.chest_o.slider1.value))
        config.set('offset', 'chest_pos_2', str(self.root.ids.chest_o.slider2.value))
        config.set('offset', 'lshoulder_pos_1', str(self.root.ids.lshoulder_o.slider1.value))
        config.set('offset', 'lshoulder_pos_2', str(self.root.ids.lshoulder_o.slider2.value))
        config.set('offset', 'rshoulder_pos_1', str(self.root.ids.rshoulder_o.slider1.value))
        config.set('offset', 'rshoulder_pos_2', str(self.root.ids.rshoulder_o.slider2.value))
        config.set('offset', 'lupperarm_pos_1', str(self.root.ids.lupperarm_o.slider1.value))
        config.set('offset', 'lupperarm_pos_2', str(self.root.ids.lupperarm_o.slider2.value))
        config.set('offset', 'rupperarm_pos_1', str(self.root.ids.rupperarm_o.slider1.value))
        config.set('offset', 'rupperarm_pos_2', str(self.root.ids.rupperarm_o.slider2.value))
        config.set('offset', 'head_pos_1', str(self.root.ids.head_o.slider1.value))
        config.set('offset', 'head_pos_2', str(self.root.ids.head_o.slider2.value))

        config.add_section('devices')
        for k, v in self.devices_list.items():
            config.set('devices', k, str(v['role']))
            
        config.add_section('devices_mode')
        for k, v in self.devices_list.items():
            config.set('devices_mode', k, str(v['mode']))
            
        config.add_section('devices_connect')
        for k, v in self.devices_list.items():
            config.set('devices_connect', k, str(int(v['connect'])))
            
        config.add_section('devices_power')
        for k, v in self.devices_list.items():
            config.set('devices_power', k, str(v['power']))
            
        config.add_section('devices_sleep')
        for k, v in self.devices_list.items():
            config.set('devices_sleep', k, str(int(v['sleep'])))

        sections = ['lfoot', 'rfoot', 'lshin', 'rshin', 'lthigh', 'rthigh', 
                    'waist', 'chest', 'lshoulder', 'rshoulder', 'lupperarm', 'rupperarm']
        for section in sections:
            for item in config.items(section):
                if item[1] == '':
                    config.set(section, item[0], '0')

        with open(file, 'w') as f:
            config.write(f)
            
        filename = file.split('\\')[-1]
        self.root.ids.save_load_text.text = '{} saved'.format(filename)
        self.update_settings(file)
    
    @mainthread    
    def load(self, file):
        if os.path.isfile(file):
            try:
                config = ConfigParser()
                config.read(file)
                
                if config.get('version', 'version') != VERSION:
                    raise
                
                self.root.ids.lfoot_t.tx.text = config.get('lfoot', 'x')
                self.root.ids.lfoot_t.ty.text = config.get('lfoot', 'y')
                self.root.ids.lfoot_t.tz.text = config.get('lfoot', 'z')

                self.root.ids.rfoot_t.tx.text = config.get('rfoot', 'x')
                self.root.ids.rfoot_t.ty.text = config.get('rfoot', 'y')
                self.root.ids.rfoot_t.tz.text = config.get('rfoot', 'z')

                self.root.ids.lshin_t.tx.text = config.get('lshin', 'x')
                self.root.ids.lshin_t.ty.text = config.get('lshin', 'y')
                self.root.ids.lshin_t.tz.text = config.get('lshin', 'z')

                self.root.ids.rshin_t.tx.text = config.get('rshin', 'x')
                self.root.ids.rshin_t.ty.text = config.get('rshin', 'y')
                self.root.ids.rshin_t.tz.text = config.get('rshin', 'z')

                self.root.ids.lthigh_t.tx.text = config.get('lthigh', 'x')
                self.root.ids.lthigh_t.ty.text = config.get('lthigh', 'y')
                self.root.ids.lthigh_t.tz.text = config.get('lthigh', 'z')

                self.root.ids.rthigh_t.tx.text = config.get('rthigh', 'x')
                self.root.ids.rthigh_t.ty.text = config.get('rthigh', 'y')
                self.root.ids.rthigh_t.tz.text = config.get('rthigh', 'z')

                self.root.ids.waist_t.tx.text = config.get('waist', 'x')
                self.root.ids.waist_t.ty.text = config.get('waist', 'y')
                self.root.ids.waist_t.tz.text = config.get('waist', 'z')
                
                self.root.ids.chest_t.tx.text = config.get('chest', 'x')
                self.root.ids.chest_t.ty.text = config.get('chest', 'y')
                self.root.ids.chest_t.tz.text = config.get('chest', 'z')
                
                self.root.ids.lshoulder_t.tx.text = config.get('lshoulder', 'x')
                self.root.ids.lshoulder_t.ty.text = config.get('lshoulder', 'y')
                self.root.ids.lshoulder_t.tz.text = config.get('lshoulder', 'z')
                
                self.root.ids.rshoulder_t.tx.text = config.get('rshoulder', 'x')
                self.root.ids.rshoulder_t.ty.text = config.get('rshoulder', 'y')
                self.root.ids.rshoulder_t.tz.text = config.get('rshoulder', 'z')
                
                self.root.ids.lupperarm_t.tx.text = config.get('lupperarm', 'x')
                self.root.ids.lupperarm_t.ty.text = config.get('lupperarm', 'y')
                self.root.ids.lupperarm_t.tz.text = config.get('lupperarm', 'z')
                
                self.root.ids.rupperarm_t.tx.text = config.get('rupperarm', 'x')
                self.root.ids.rupperarm_t.ty.text = config.get('rupperarm', 'y')
                self.root.ids.rupperarm_t.tz.text = config.get('rupperarm', 'z')

                self.root.ids.shin_h.slider.value = float(config.get('parameter', 'shin_h'))
                self.root.ids.thigh_h.slider.value = float(config.get('parameter', 'thigh_h'))
                self.root.ids.lback_h.slider.value = float(config.get('parameter', 'lback_h'))
                self.root.ids.uback_h.slider.value = float(config.get('parameter', 'uback_h'))
                self.root.ids.head_h.slider.value = float(config.get('parameter', 'head_h'))
                self.root.ids.shoulder_h.slider.value = float(config.get('parameter', 'shoulder_h'))
                self.root.ids.hip_width_h.slider.value = float(config.get('parameter', 'hip_width_h'))
                self.root.ids.shoulder_width_h.slider.value = float(config.get('parameter', 'shoulder_width_h'))
                self.root.ids.vscale.slider.value = float(config.get('parameter', 'vscale'))
                self.root.ids.hscale.slider.value = float(config.get('parameter', 'hscale'))
                self.root.ids.foot_sensor_h.slider.value = float(config.get('parameter', 'foot_sensor_h'))
                self.root.ids.shin_sensor_h.slider.value = float(config.get('parameter', 'shin_sensor_h'))
                self.root.ids.thigh_sensor_h.slider.value = float(config.get('parameter', 'thigh_sensor_h'))
                self.root.ids.waist_sensor_h.slider.value = float(config.get('parameter', 'waist_sensor_h'))
                self.root.ids.chest_sensor_h.slider.value = float(config.get('parameter', 'chest_sensor_h'))
                self.root.ids.shoulder_sensor_h.slider.value = float(config.get('parameter', 'shoulder_sensor_h'))
                self.root.ids.upperarm_sensor_h.slider.value = float(config.get('parameter', 'upperarm_sensor_h'))
                self.root.ids.floor_offset.slider.value = float(config.get('parameter', 'floor_offset'))
                self.root.ids.override_feet_en_check.switch.active = int(config.get('parameter', 'override_feet_en_check'))
                
                self.root.ids.feet_en_check.switch.active = int(config.get('activation', 'feet_en_check'))
                self.root.ids.shin_en_check.switch.active = int(config.get('activation', 'shin_en_check'))
                self.root.ids.thigh_en_check.switch.active = int(config.get('activation', 'thigh_en_check'))
                self.root.ids.waist_en_check.switch.active = int(config.get('activation', 'waist_en_check'))
                self.root.ids.chest_en_check.switch.active = int(config.get('activation', 'chest_en_check'))
                self.root.ids.shoulder_en_check.switch.active = int(config.get('activation', 'shoulder_en_check'))
                self.root.ids.upperarm_en_check.switch.active = int(config.get('activation', 'upperarm_en_check'))
                
                self.root.ids.lfoot_o.slider1.value = float(config.get('offset', 'lfoot_pos_1'))
                self.root.ids.lfoot_o.slider2.value = float(config.get('offset', 'lfoot_pos_2'))
                self.root.ids.rfoot_o.slider1.value = float(config.get('offset', 'rfoot_pos_1'))
                self.root.ids.rfoot_o.slider2.value = float(config.get('offset', 'rfoot_pos_2'))
                self.root.ids.lshin_o.slider1.value = float(config.get('offset', 'lshin_pos_1'))
                self.root.ids.lshin_o.slider2.value = float(config.get('offset', 'lshin_pos_2'))
                self.root.ids.rshin_o.slider1.value = float(config.get('offset', 'rshin_pos_1'))
                self.root.ids.rshin_o.slider2.value = float(config.get('offset', 'rshin_pos_2'))
                self.root.ids.lthigh_o.slider1.value = float(config.get('offset', 'lthigh_pos_1'))
                self.root.ids.lthigh_o.slider2.value = float(config.get('offset', 'lthigh_pos_2'))
                self.root.ids.rthigh_o.slider1.value = float(config.get('offset', 'rthigh_pos_1'))
                self.root.ids.rthigh_o.slider2.value = float(config.get('offset', 'rthigh_pos_2'))
                self.root.ids.waist_o.slider1.value = float(config.get('offset', 'waist_pos_1'))
                self.root.ids.waist_o.slider2.value = float(config.get('offset', 'waist_pos_2'))
                self.root.ids.chest_o.slider1.value = float(config.get('offset', 'chest_pos_1'))
                self.root.ids.chest_o.slider2.value = float(config.get('offset', 'chest_pos_2'))
                self.root.ids.lshoulder_o.slider1.value = float(config.get('offset', 'lshoulder_pos_1'))
                self.root.ids.lshoulder_o.slider2.value = float(config.get('offset', 'lshoulder_pos_2'))
                self.root.ids.rshoulder_o.slider1.value = float(config.get('offset', 'rshoulder_pos_1'))
                self.root.ids.rshoulder_o.slider2.value = float(config.get('offset', 'rshoulder_pos_2'))
                self.root.ids.lupperarm_o.slider1.value = float(config.get('offset', 'lupperarm_pos_1'))
                self.root.ids.lupperarm_o.slider2.value = float(config.get('offset', 'lupperarm_pos_2'))
                self.root.ids.rupperarm_o.slider1.value = float(config.get('offset', 'rupperarm_pos_1'))
                self.root.ids.rupperarm_o.slider2.value = float(config.get('offset', 'rupperarm_pos_2'))
                self.root.ids.head_o.slider1.value = float(config.get('offset', 'head_pos_1'))
                self.root.ids.head_o.slider2.value = float(config.get('offset', 'head_pos_2'))

                for k in config.items('devices'):
                    self.devices_list[k[0]] = {}
                    self.devices_list[k[0]]['role'] = k[1]
                    if k[0] + '_role_role' in self.root.ids.keys():
                        self.root.ids[k[0] + '_role_role'].text = k[1]
                    
                for k in config.items('devices_mode'):
                    self.devices_list[k[0]]['mode'] = k[1]
                    if k[0] + '_role_mode' in self.root.ids.keys():
                        self.root.ids[k[0] + '_role_mode'].text = k[1]
                    
                for k in config.items('devices_connect'):
                    self.devices_list[k[0]]['connect'] = int(k[1])
                    if k[0] + '_role_connect' in self.root.ids.keys():
                        self.root.ids[k[0] + '_role_connect'].active = bool(int(k[1]))
                        
                for k in config.items('devices_power'):
                    self.devices_list[k[0]]['power'] = k[1]
                    if k[0] + '_role_power' in self.root.ids.keys():
                        self.root.ids[k[0] + '_role_power'].text = k[1]
                        
                for k in config.items('devices_sleep'):
                    self.devices_list[k[0]]['sleep'] = int(k[1])
                    if k[0] + '_role_sleep' in self.root.ids.keys():
                        self.root.ids[k[0] + '_role_sleep'].active = bool(int(k[1]))
                
                filename = file.split('\\')[-1]
                self.root.ids.save_load_text.text = '{} loaded'.format(filename)
                self.update_settings(file)
                
            except:
                self.root.ids.save_load_text.text = 'Invalid file or version'
                
        else:
            self.root.ids.save_load_text.text = 'Invalid file or version'
            
    def update_settings(self, filepath):        
        config = ConfigParser()
        
        config.add_section('last_settings')
        config.set('last_settings', 'path', filepath)
        
        with open(self.settings_bak, 'w') as f:
            config.write(f)

    def on_start(self):
        self.title = 'IMU FBT Server'
        
        dir_path = os.path.join(os.path.expanduser('~'),
                                'Documents', 'imuFBT')
        if not os.path.isdir(dir_path):
            os.mkdir(dir_path)
        self.settings_bak = os.path.join(dir_path, 'imuFBT_settings.cfg')
        
        if os.path.isfile(self.settings_bak):
            try:
                config = ConfigParser()
                config.read(self.settings_bak)
                self.load(config.get('last_settings', 'path'))
            except:
                pass
            
        self.bridgePort = 0
            
        self.backend_run = True
        self.backend_process = threading.Thread(target=self.backend, args=())
        self.backend_process.start()
        
        self.clock1 = Clock.schedule_interval(self.com_port_scanner, 3)
        
        self.clock2 = Clock.schedule_once(self.delay_cb, 0.5)
        
    def backend(self):
        exe_path = resource_path(os.path.join('backend', 'imuFBTServerBackend.exe'))
        while self.backend_run:
            self.backend_exe = subprocess.Popen([exe_path], creationflags = subprocess.CREATE_NO_WINDOW)
            self.backend_exe.wait()
            time.sleep(1)
        
    def delay_cb(self, dt):
        self.thread_run = True
        self.thread_process = threading.Thread(target=self.udp, args=())
        self.thread_process.start()

        self.broad_run = True
        self.broad_process = threading.Thread(target=self.broadudp, args=())
        self.broad_process.start()
        
    def on_stop(self):
        try:
            self.clock1.cancel()
        except:
            pass
        
        try:
            self.clock2.cancel()
        except:
            pass
        
        self.wifi_thread_run = False
        try:
            self.wifi_thread_process.join()
        except:
            pass
        
        self.calibrate_run = False
        try:
            self.calibrate_process.join()
        except:
            pass
        
        self.broad_run = False
        try:
            self.broad_process.join()
        except:
            pass

        self.thread_run = False
        try:
            self.thread_process.join()
        except:
            pass
        
        self.backend_run = False
        try:
            self.backend_exe.terminate()
            self.backend_process.join()
        except:
            pass
        
        self.fLock.close()
        os.remove(self.lock_file)

    def build(self):
        dir_path = os.path.join(os.path.expanduser('~'),
                                'Documents', 'imuFBT')
        if not os.path.isdir(dir_path):
            os.mkdir(dir_path)
        self.lock_file = os.path.join(dir_path, 'lock')
        try:
            os.remove(self.lock_file)
        except PermissionError:
            return sys.exit()
        except FileNotFoundError:
            pass
        self.fLock = open(self.lock_file, 'w')
        return Builder.load_file(resource_path('main.kv'))


if __name__ == '__main__':
    ImuFbtServer().run()
