m9cd0n9ld/IMU-VR-Full-Body-Tracker/steamvr_openvr_driver/driver_imuFBT/headers/TrackerDriver.h

#pragma once

#include <Globals.h>
#include <openvr_driver.h>

using namespace vr;

class TrackerDriver : public ITrackedDeviceServerDriver
{

public:
	virtual void SetTrackerIndex(int32_t TrackerIndex);
	virtual void SetModel(std::string model);
	virtual void SetVersion(std::string version);
	virtual EVRInitError Activate(TrackedDeviceIndex_t unObjectId);
	virtual void Deactivate();
	virtual void EnterStandby();
	void* GetComponent(const char* pchComponentNameAndVersion);
	virtual void PowerOff();
	virtual void DebugRequest(const char* pchRequest, char* pchResponseBuffer, uint32_t unResponseBufferSize);
	virtual DriverPose_t GetPose();
	void RunFrame();

private:
	float map(float x, float in_min = -32767, float in_max = 32767, float out_min = -1, float out_max = 1) {
		return (x - in_min) * (out_max - out_min) / (in_max - in_min) + out_min;
	}

	int32_t TrackerIndex = 0;
	std::string model = "";
	std::string version = "";

	TrackedDeviceIndex_t m_unObjectId = k_unTrackedDeviceIndexInvalid;
	PropertyContainerHandle_t m_ulPropertyContainer = k_ulInvalidPropertyContainer;
};
